yuriyKazan/Environment-logger/hardware/kicad/env-logger.kicad_sch

## KiCad design hardware/kicad/env-logger.kicad_sch (2026-10-05)

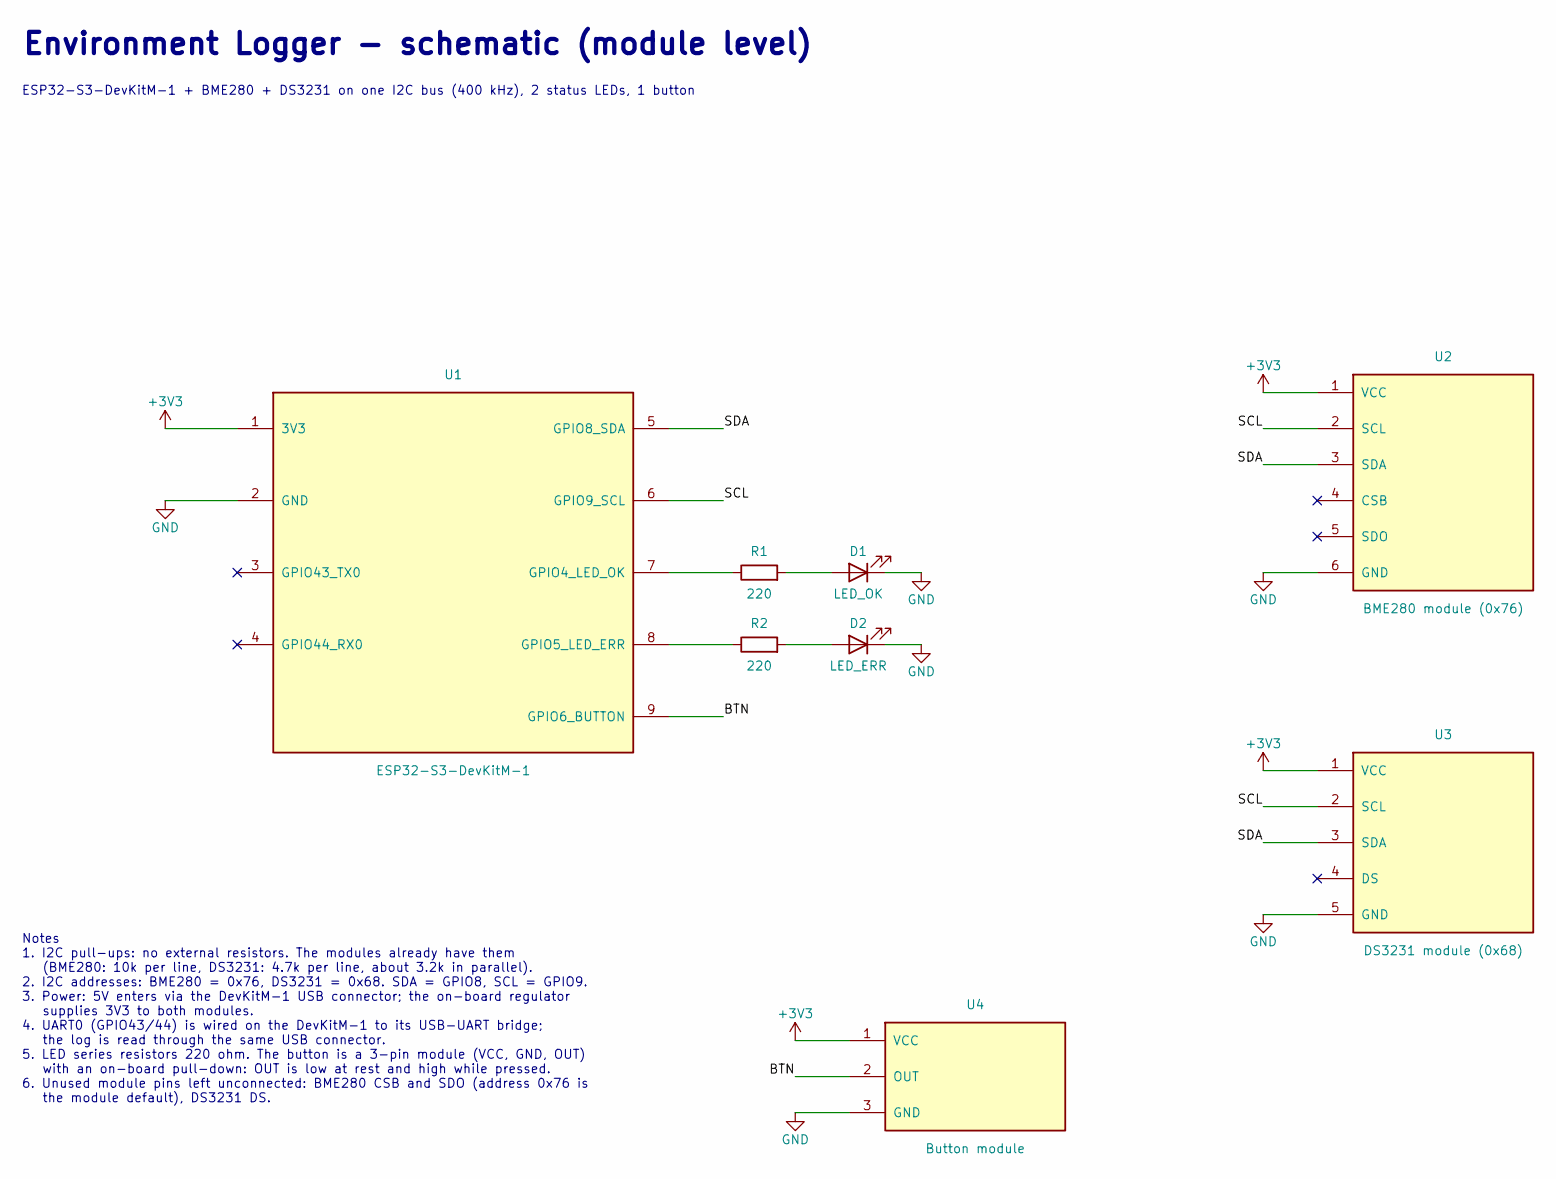
[picture p9: schematic env-logger.kicad_sch]

Parts:
D1: LED_OK
D2: LED_ERR
R1, R2: 220
U1: ESP32-S3-DevKitM-1
U2: BME280 module (0x76)
U3: DS3231 module (0x68)
U4: Button module

Connections:
+3V3: U1.1 (3V3), U2.1 (VCC), U3.1 (VCC), U4.1 (VCC)
BTN: U1.9 (GPIO6_BUTTON), U4.2 (OUT)
GND: D1.1 (K), D2.1 (K), U1.2 (GND), U2.6 (GND), U3.5 (GND), U4.3 (GND)
unnamed: D1.2 (A), R1.2
unnamed: D2.2 (A), R2.2
unnamed: R1.1, U1.7 (GPIO4_LED_OK)
unnamed: R2.1, U1.8 (GPIO5_LED_ERR)
SCL: U1.6 (GPIO9_SCL), U2.2 (SCL), U3.2 (SCL)
SDA: U1.5 (GPIO8_SDA), U2.3 (SDA), U3.3 (SDA)

Notes on the sheet:
Environment Logger - schematic (module level)
Notes 1. I2C pull-ups: no external resistors. The modules already have them (BME280: 10k per line, DS3231: 4.7k per line, about 3.2k in parallel). 2. I2C addresses: BME280 = 0x76, DS3231 = 0x68. SDA = GPIO8, SCL = GPIO9. 3. Power: 5V enters via the DevKitM-1 USB connector; the on-board regulator su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
ESP32-S3-DevKitM-1 + BME280 + DS3231 on one I2C bus (400 kHz), 2 status LEDs, 1 button
